openxc/reference-vi/electrical/img/BT_Endurance_Histogram_012613_lrg.png

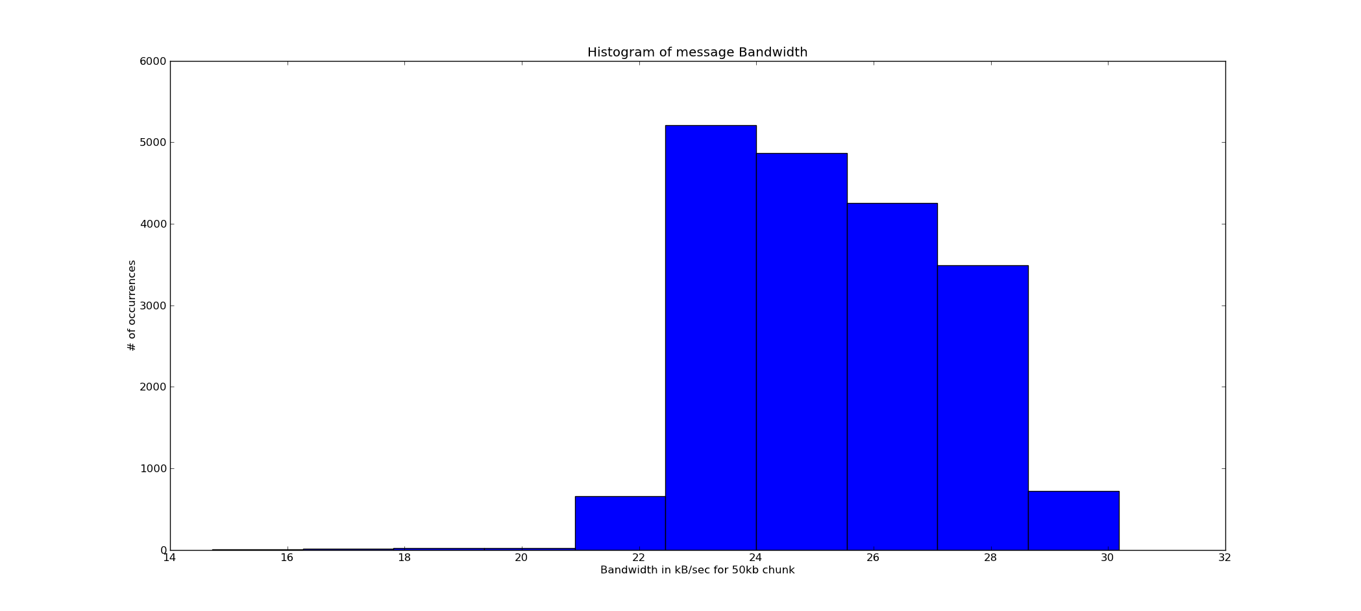
electrical/img/BT_Endurance_Histogram_012613_lrg.png
