openxc/reference-vi/electrical/sources/vehicle-interface.brd.png

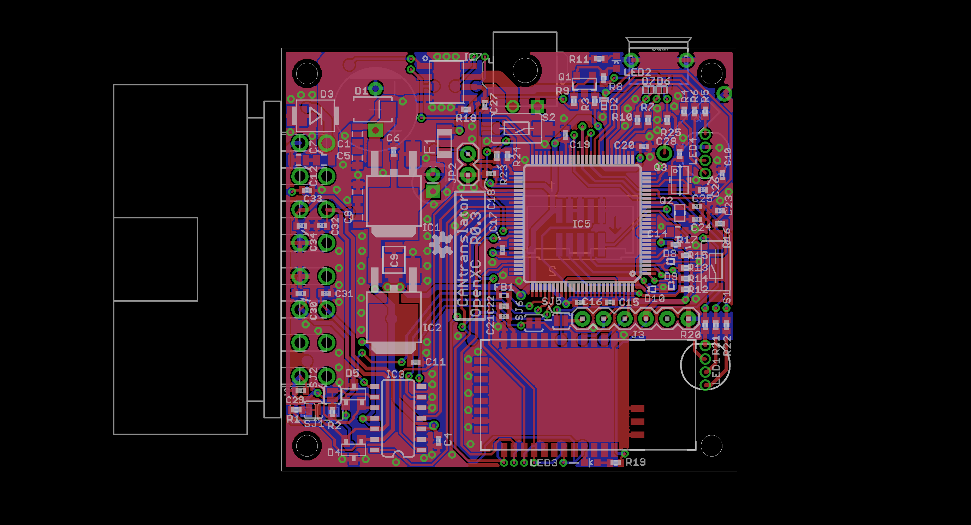
electrical/sources/vehicle-interface.brd.png
