openxc/reference-vi/static/images/vi-back-square.jpg

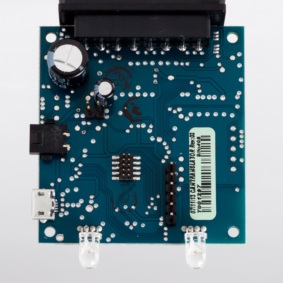
static/images/vi-back-square.jpg
